floookay/pluckey/case/sandwich/layers/case-bottom layer 2.dxf

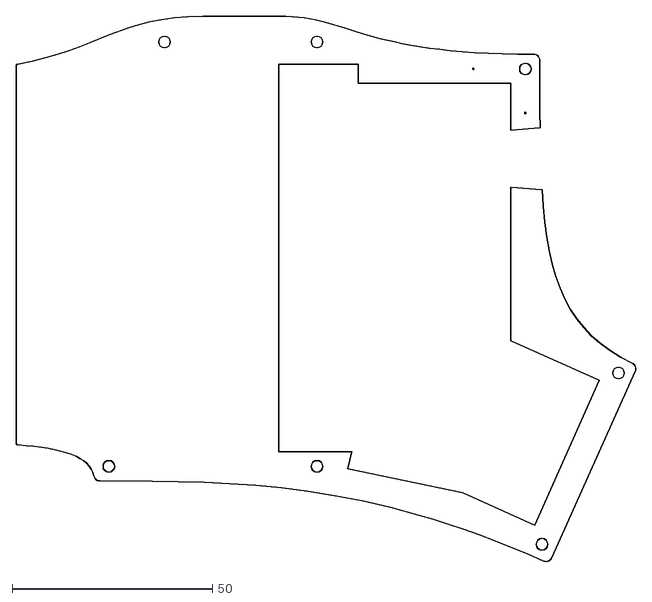
[picture p15: CAD file, 2021-10-02]
case/sandwich/layers/case-bottom layer 2.dxf
154.8 x 136.2
