floookay/pluckey/case/sandwich/layers/case-plate layer.dxf

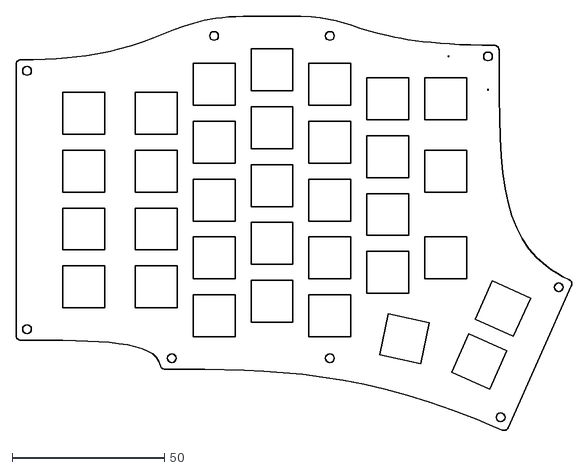
[picture p16: CAD file, 2021-10-02]
case/sandwich/layers/case-plate layer.dxf
182.9 x 136.2
