floookay/pluckey/case/sandwich/layers/case-bottom layer 4.dxf

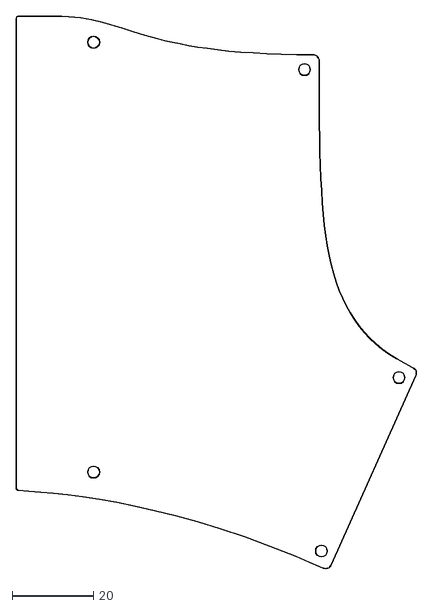
[picture p17: CAD file, 2021-10-02]
case/sandwich/layers/case-bottom layer 4.dxf
98.7 x 136.2
