floookay/pluckey/case/sandwich/layers/case-middle layer port edge.dxf

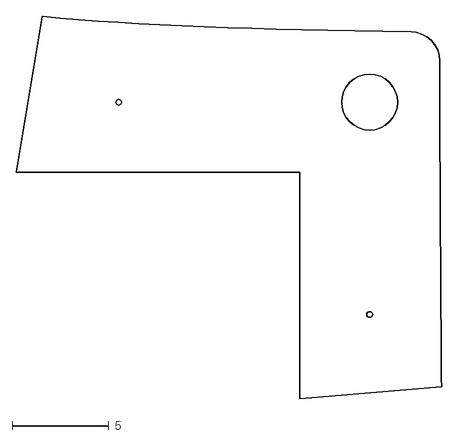
[picture p18: CAD file, 2021-10-02]
case/sandwich/layers/case-middle layer port edge.dxf
22.0 x 19.8
