floookay/pluckey/case/sandwich/layers/case-bottom layer 3.dxf

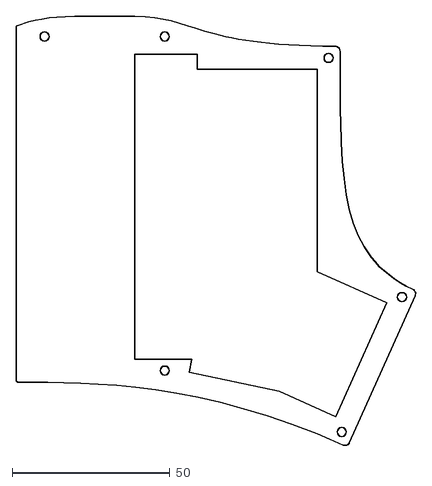
[picture p19: CAD file, 2021-10-02]
case/sandwich/layers/case-bottom layer 3.dxf
126.8 x 136.2
