floookay/pluckey/case/sandwich/layers/case-middle layer 2.dxf

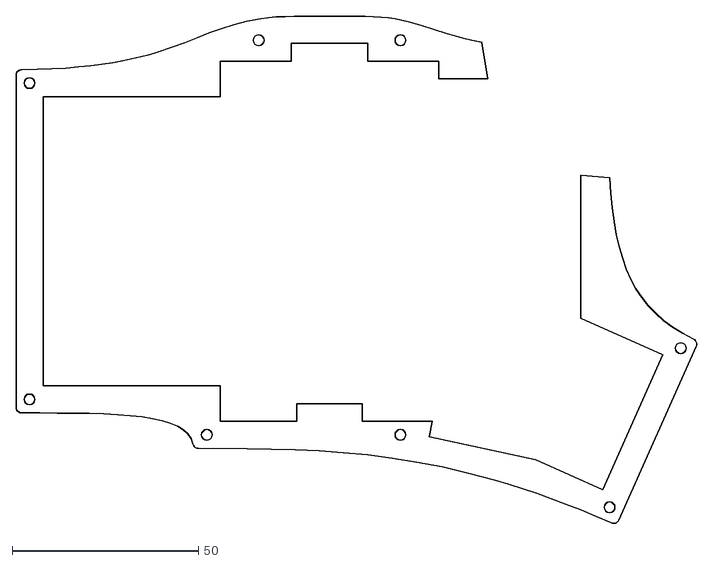
[picture p20: CAD file, 2021-10-02]
case/sandwich/layers/case-middle layer 2.dxf
182.9 x 136.2
